TrevorRawlings/LED_timer/mplab/LED.X/configuration_bits.c

/******************************************************************************/
/* Files to Include                                                           */
/******************************************************************************/

#if defined(__XC)
    #include <xc.h>         /* XC8 General Include File */
#elif defined(HI_TECH_C)
    #include <htc.h>        /* HiTech General Include File */
#elif defined(__18CXX)
    #include <p18cxxx.h>    /* C18 General Include File */
#endif

/******************************************************************************/
/* Configuration Bits                                                         */
/*                                                                            */
/* Refer to 'HI-TECH PICC and PICC18 Toolchains > PICC18 Configuration        */
/* Settings' under Help > Contents in MPLAB X IDE for available PIC18         */
/* Configuration Bit Settings for the correct macros when using the C18       */
/* compiler.  When using the Hi-Tech PICC18 compiler, refer to the compiler   */
/* manual.pdf in the compiler installation doc directory section on           */
/* 'Configuration Fuses'.  The device header file in the HiTech PICC18        */
/* compiler installation directory contains the available macros to be        */
/* embedded.  The XC8 compiler contains documentation on the configuration    */
/* bit macros within the compiler installation /docs folder in a file called  */
/* pic18_chipinfo.html.                                                       */
/*                                                                            */
/* For additional information about what the hardware configurations mean in  */
/* terms of device operation, refer to the device datasheet.                  */
/*                                                                            */
/* General C18/XC8 syntax for configuration macros:                           */
/* #pragma config <Macro Name>=<Setting>, <Macro Name>=<Setting>, ...         */
/*                                                                            */
/* General HiTech PICC18 syntax:                                              */
/* __CONFIG(n,x);                                                             */
/*                                                                            */
/* n is the config word number and x represents the anded macros from the     */
/* device header file in the PICC18 compiler installation include directory.  */
/*                                                                            */
/* A feature of MPLAB X is the 'Generate Source Code to Output' utility in    */
/* the Configuration Bits window.  Under Window > PIC Memory Views >          */
/* Configuration Bits, a user controllable configuration bits window is       */
/* available to Generate Configuration Bits source code which the user can    */
/* paste into this project.                                                   */
/*                                                                            */
/******************************************************************************/


// PIC18LF1320 Configuration Bit Settings

// 'C' source line config statements

// CONFIG1H
#pragma config OSC = EC       // Oscillator Selection bits (EC oscillator, port function on RA6)
#pragma config FSCM = OFF        // Fail-Safe Clock Monitor Enable bit (Fail-Safe Clock Monitor enabled)
#pragma config IESO = ON        // Internal External Switchover bit (Internal External Switchover mode enabled)

// CONFIG2L
#pragma config PWRT = ON        // Power-up Timer Enable bit (PWRT enabled)
#pragma config BOR = ON         // Brown-out Reset Enable bit (Brown-out Reset enabled)
// BORV = No Setting

// CONFIG2H
#pragma config WDT = OFF        // Watchdog Timer Enable bit (WDT disabled (control is placed on the SWDTEN bit))
#pragma config WDTPS = 32768    // Watchdog Timer Postscale Select bits (1:32768)

// CONFIG3H
#pragma config MCLRE = ON       // MCLR Pin Enable bit (MCLR pin enabled, RA5 input pin disabled)

// CONFIG4L
#pragma config STVR = ON        // Stack Full/Underflow Reset Enable bit (Stack full/underflow will cause Reset)
#pragma config LVP = OFF        // Low-Voltage ICSP Enable bit (Low-Voltage ICSP disabled)

// CONFIG5L
#pragma config CP0 = OFF        // Code Protection bit (Block 0 (00200-000FFFh) not code-protected)
#pragma config CP1 = OFF        // Code Protection bit (Block 1 (001000-001FFFh) not code-protected)

// CONFIG5H
#pragma config CPB = OFF        // Boot Block Code Protection bit (Boot Block (000000-0001FFh) not code-protected)
#pragma config CPD = OFF        // Data EEPROM Code Protection bit (Data EEPROM not code-protected)

// CONFIG6L
#pragma config WRT0 = OFF       // Write Protection bit (Block 0 (00200-000FFFh) not write-protected)
#pragma config WRT1 = OFF       // Write Protection bit (Block 1 (001000-001FFFh) not write-protected)

// CONFIG6H
#pragma config WRTC = OFF       // Configuration Register Write Protection bit (Configuration registers (300000-3000FFh) not write-protected)
#pragma config WRTB = OFF       // Boot Block Write Protection bit (Boot Block (000000-0001FFh) not write-protected)
#pragma config WRTD = OFF       // Data EEPROM Write Protection bit (Data EEPROM not write-protected)

// CONFIG7L
#pragma config EBTR0 = OFF      // Table Read Protection bit (Block 0 (00200-000FFFh) not protected from table reads executed in other blocks)
#pragma config EBTR1 = OFF      // Table Read Protection bit (Block 1 (001000-001FFFh) not protected from table reads executed in other blocks)

// CONFIG7H
#pragma config EBTRB = OFF      // Boot Block Table Read Protection bit (Boot Block (000000-0001FFh) not protected from table reads executed in other blocks)

// #pragma config statements should precede project file includes.
// Use project enums instead of #define for ON and OFF.

#include <xc.h>
